GBert/metering/docs/TCRT5000_mod.jpg

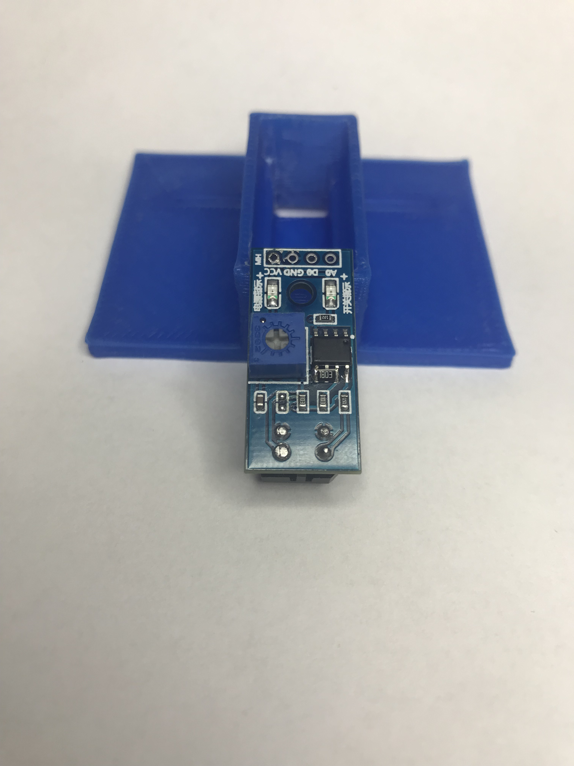
docs/TCRT5000_mod.jpg
