GBert/metering/docs/tcrt5000_off.png

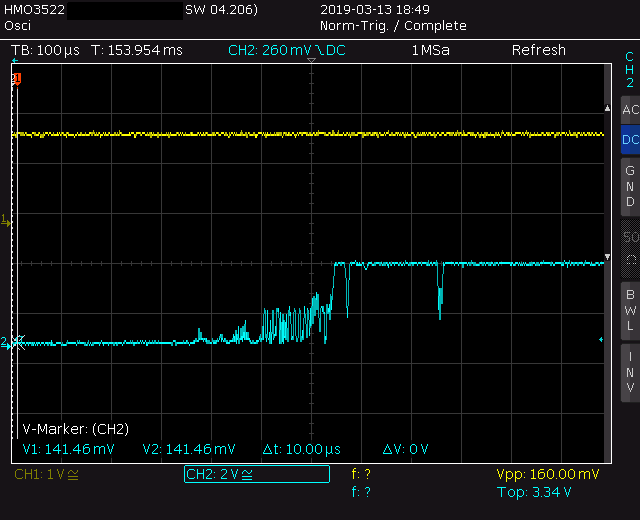
docs/tcrt5000_off.png
