GBert/metering/docs/tcrt5000_off_mod.png

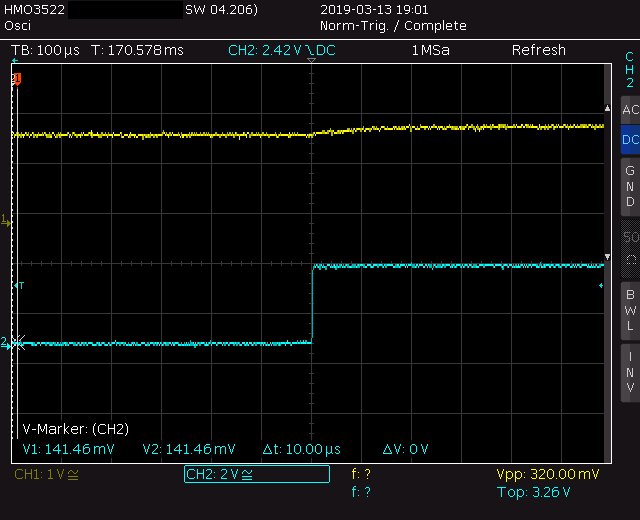
docs/tcrt5000_off_mod.png
