GBert/metering/docs/tcrt5000_on.png

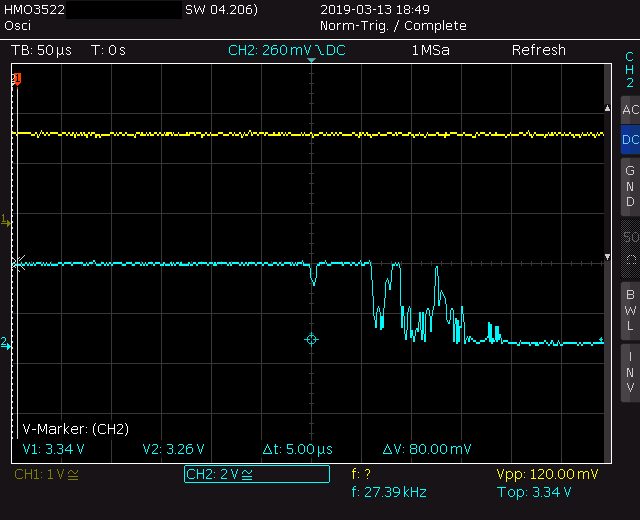
docs/tcrt5000_on.png
