GBert/metering/docs/tcrt5000_on_mod.png

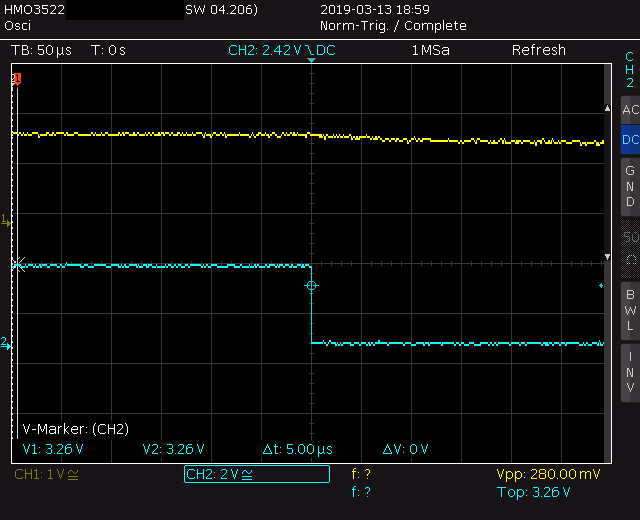
docs/tcrt5000_on_mod.png
