GBert/metering/docs/tcrt5000_pulse.png

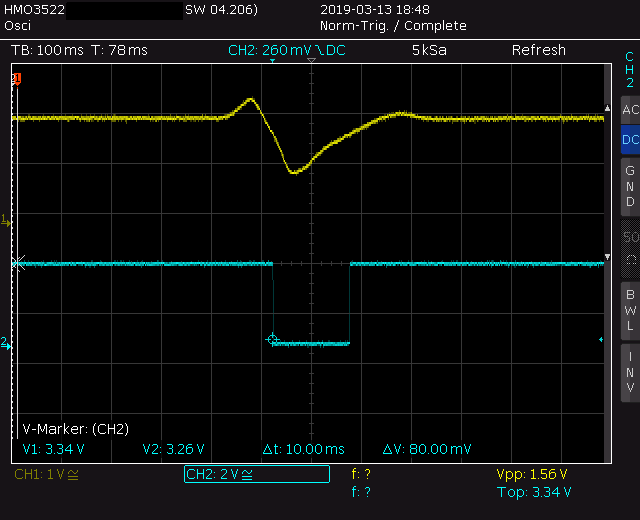
docs/tcrt5000_pulse.png
